Antz-Lee/ECE-388/Screenshots/IMG-0725.jpg

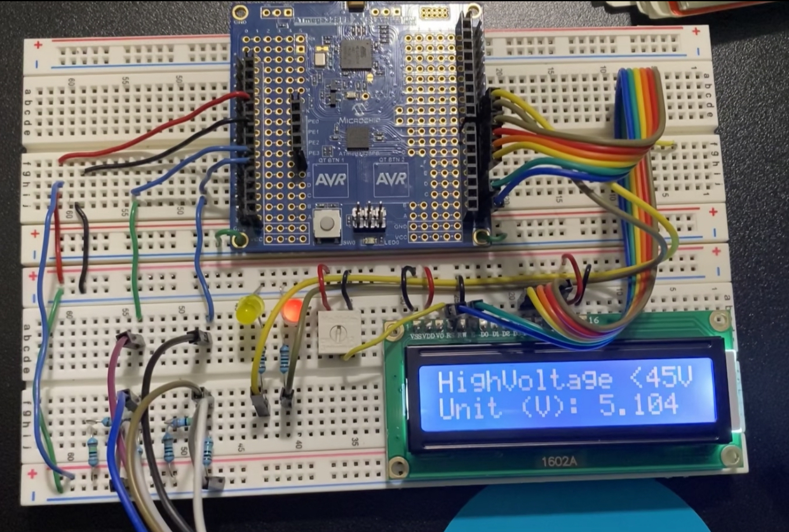
Screenshots/IMG-0725.jpg
