Antz-Lee/ECE-388/Screenshots/IMG-0727.jpg

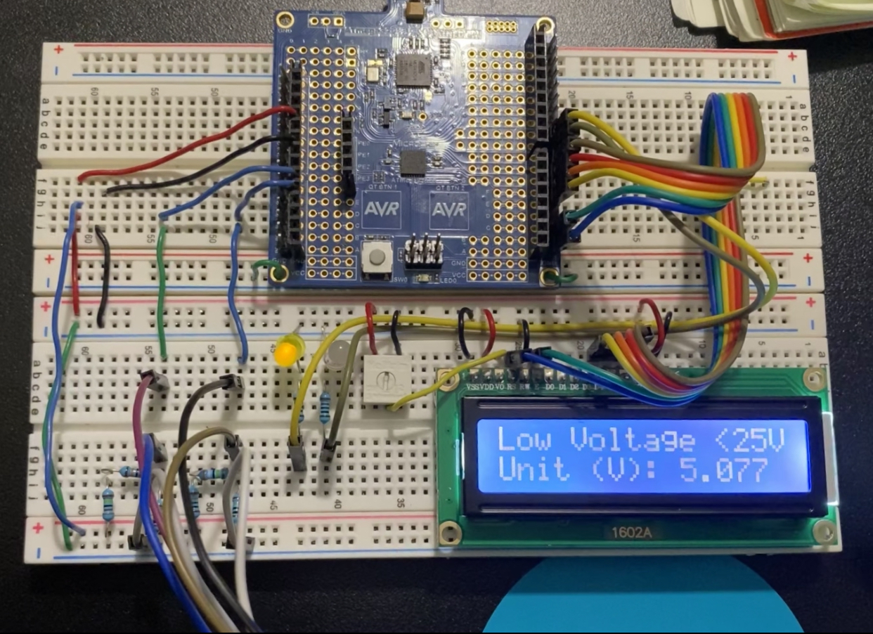
Screenshots/IMG-0727.jpg
