Antz-Lee/ECE-388/Screenshots/IMG-0720.jpg

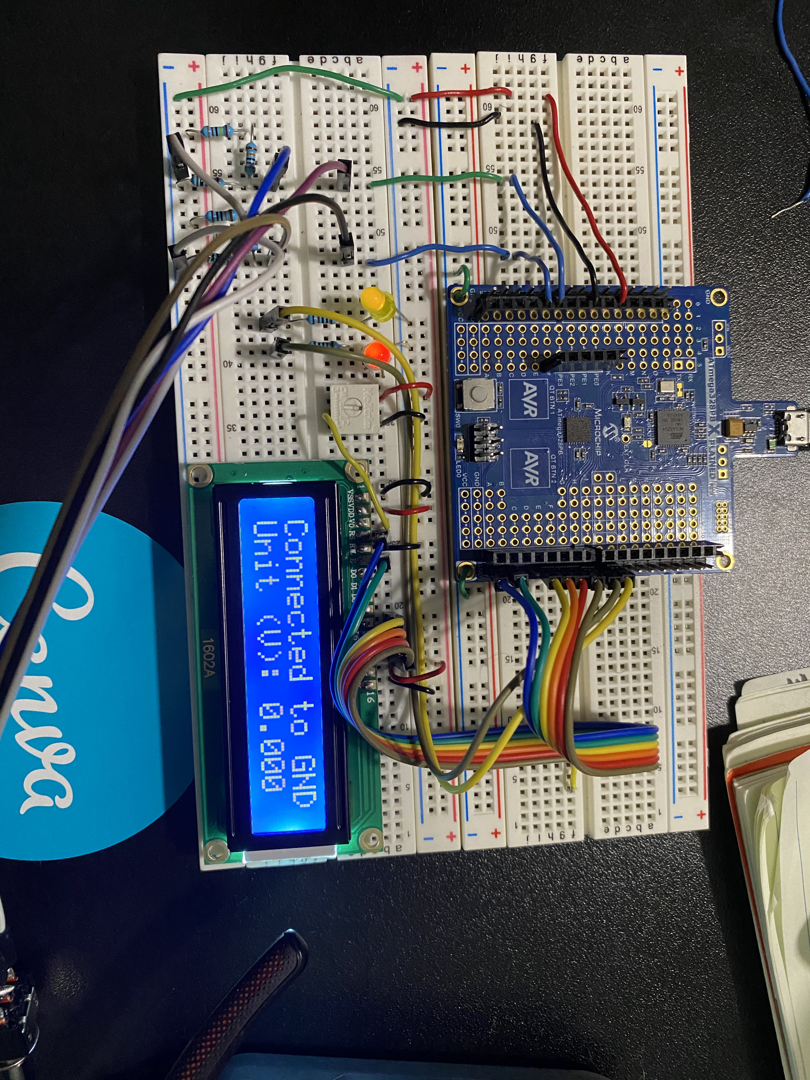
Screenshots/IMG-0720.jpg
