Antz-Lee/ECE-388/Screenshots/IMG-0722.jpg

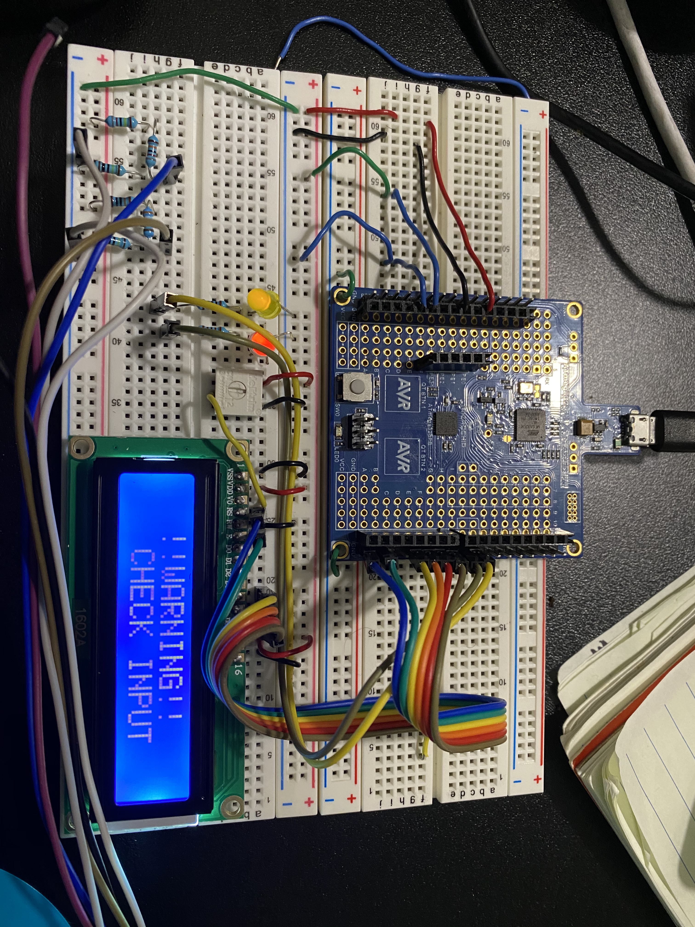
Screenshots/IMG-0722.jpg
